Engineering-3/RCMx1/board/RCMX Rev_00_BPS2_sch.pdf

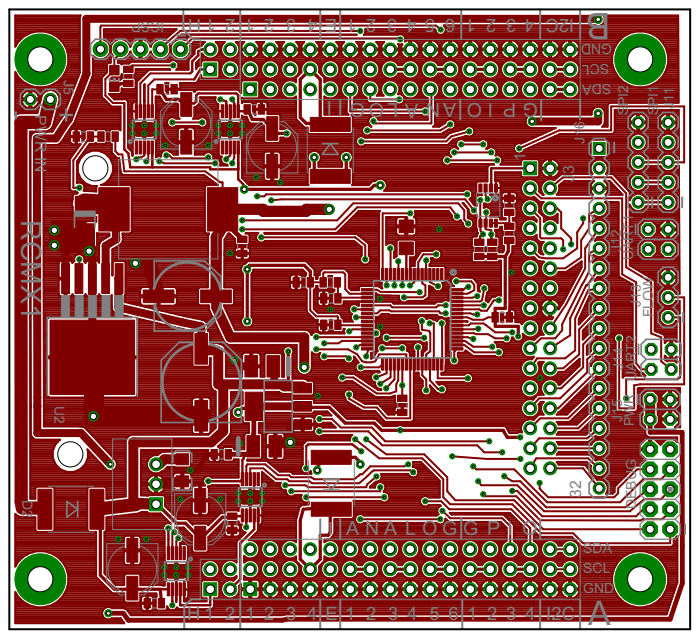
[picture p8: page 1]

J3 1 32 4G DNG LCS ADS 1 A SDA SCL GND RCMX1 -+ 2 6 1 1 I 3 4 5 4 1 2 3 4 E 1 3 4 5 1 2 3 G L NA OI P 2 4 E 2 3 6 2 3 N A L O G G P I O I O A 1 2 H 1 2 H I2CC2I PSCI PWR IN DEBUG PWR UART2 FLOW UART1 SPI2 SPI1 BA U2 J11 J5 J12 J13 J14 J15 J16 D2
