Engineering-3/RCMx1/board/RCMX Rev_00_BPS_brd.pdf

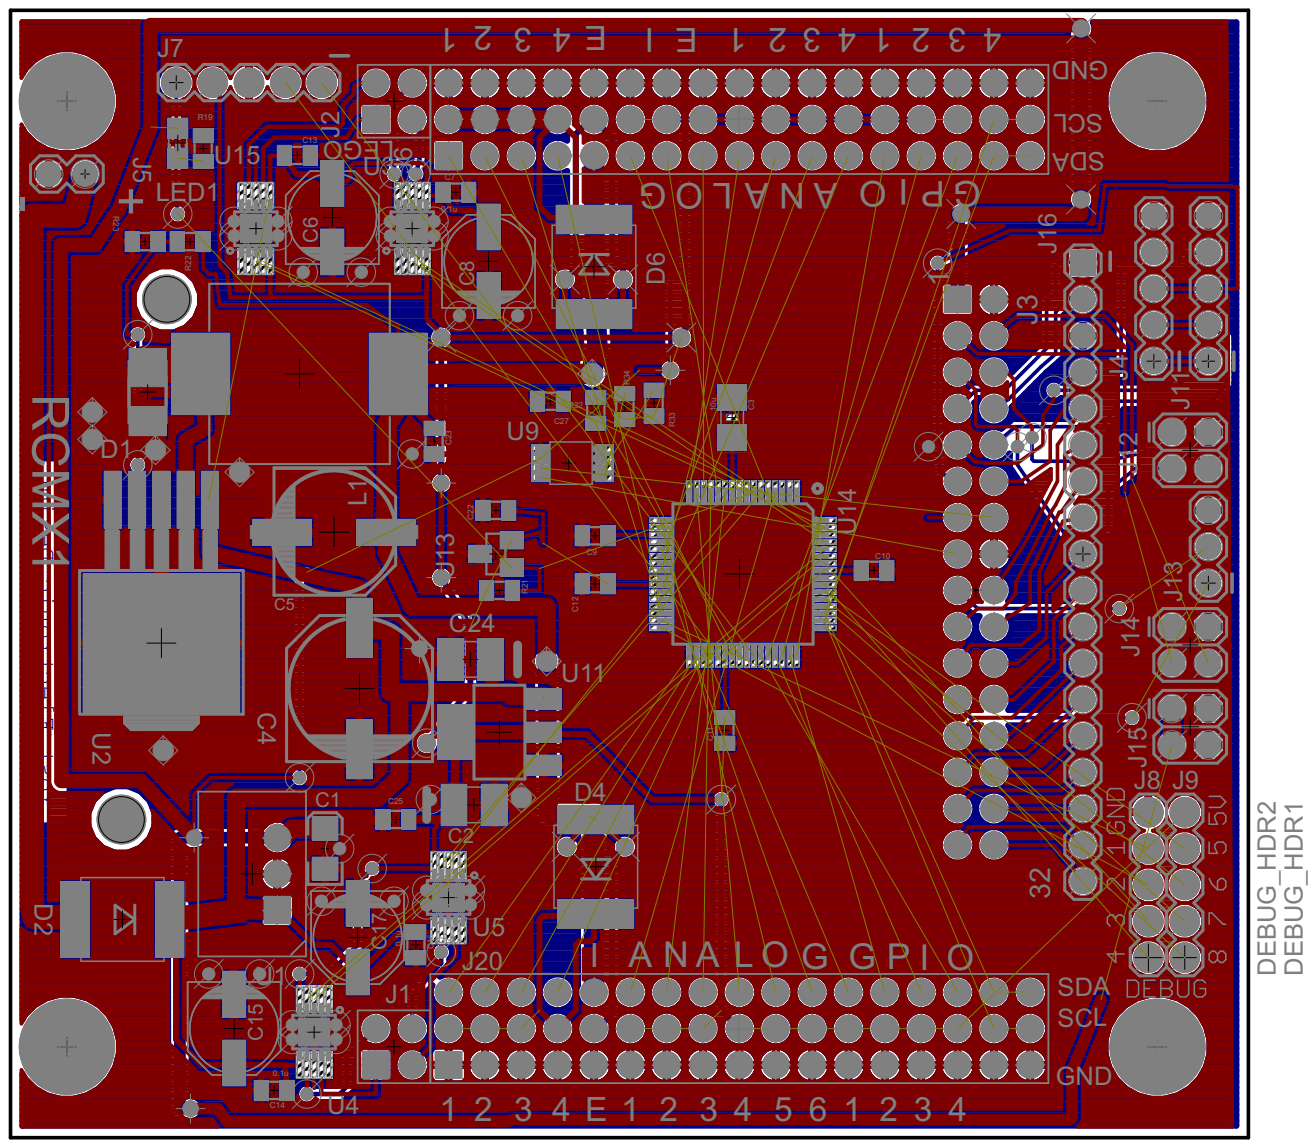
[picture p9: page 1]
