Engineering-3/RCMx1/board/RCMX Rev_00_BPS_NewSilk_silk.pdf

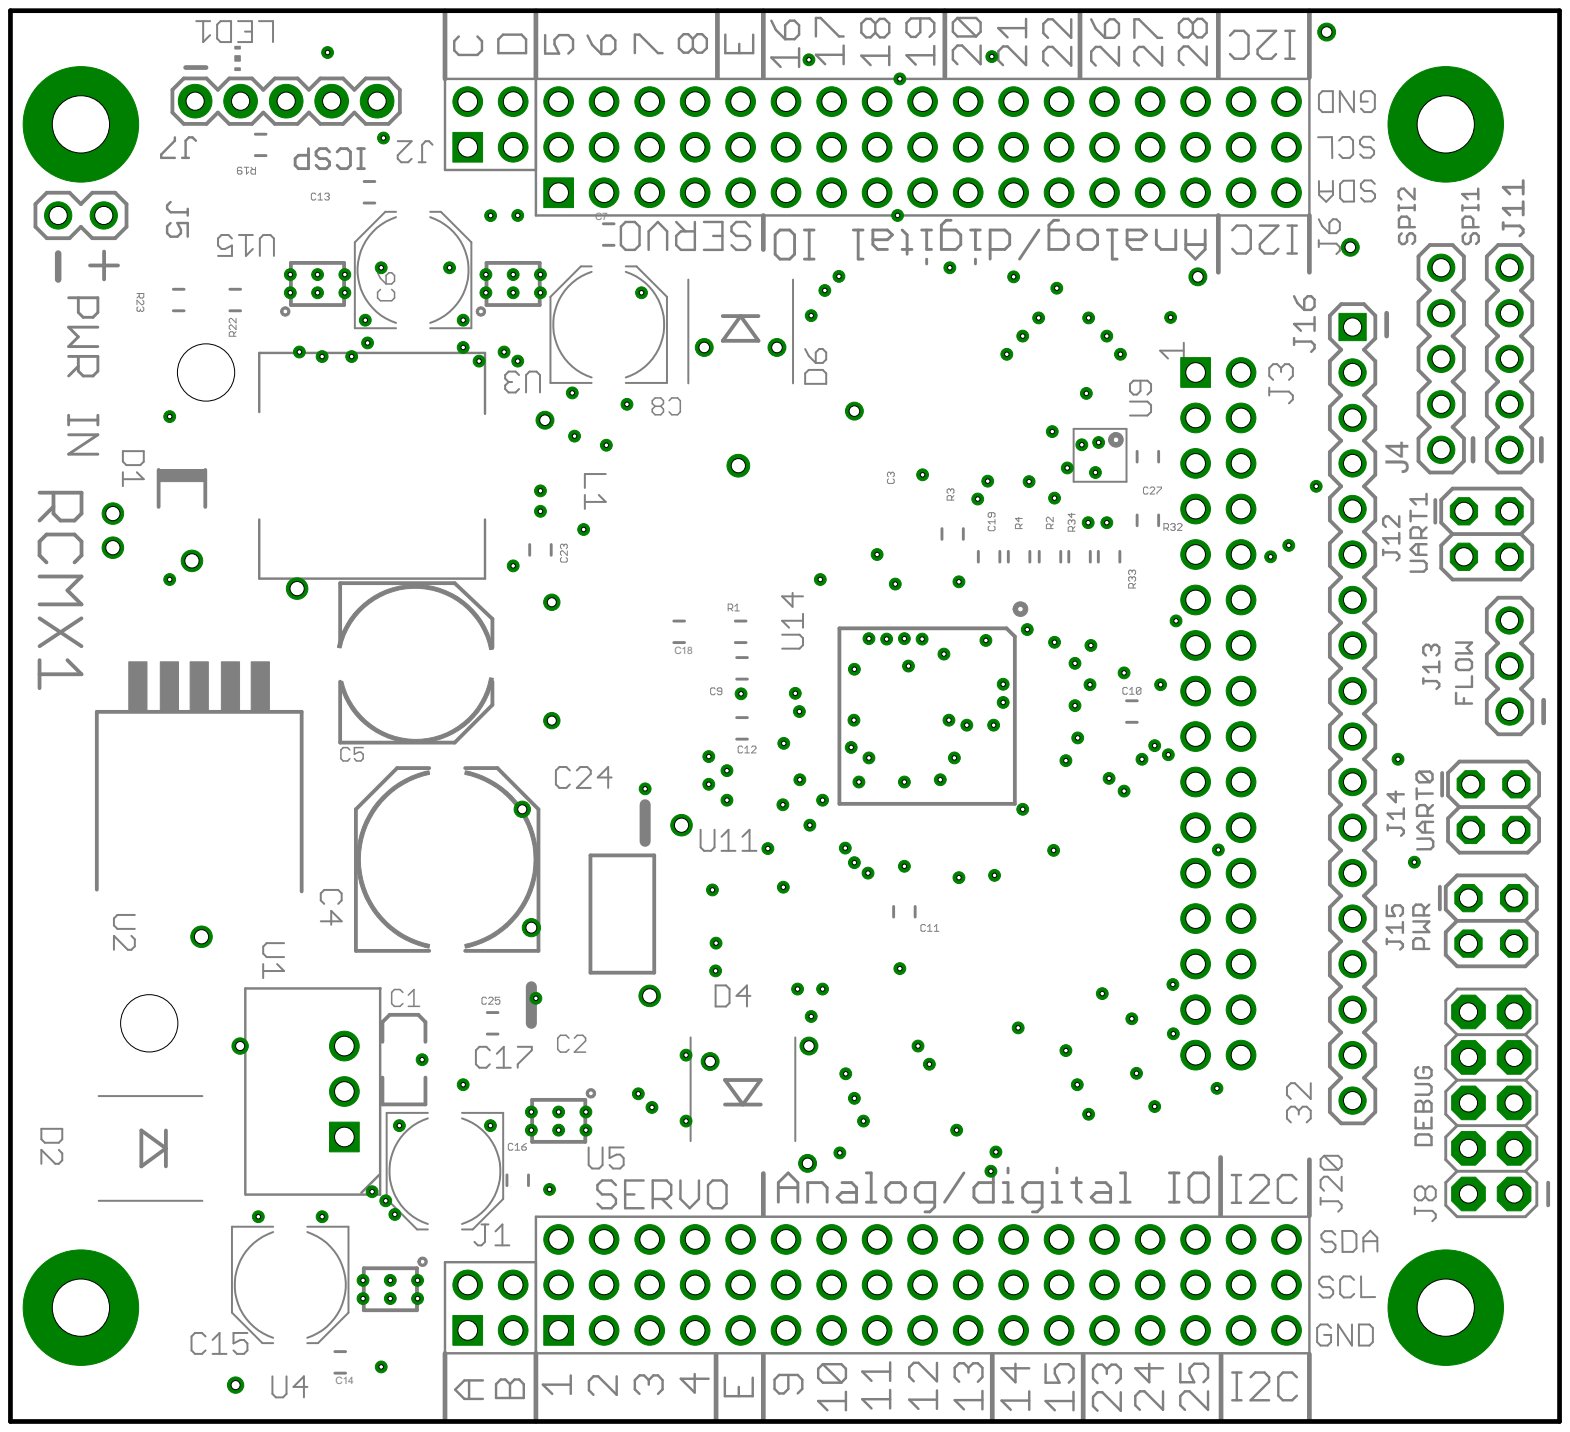
[picture p10: page 1]
