Engineering-3/RCMx1/board/RCMx1_v04/RCMx1 Rev_04_brd.pdf

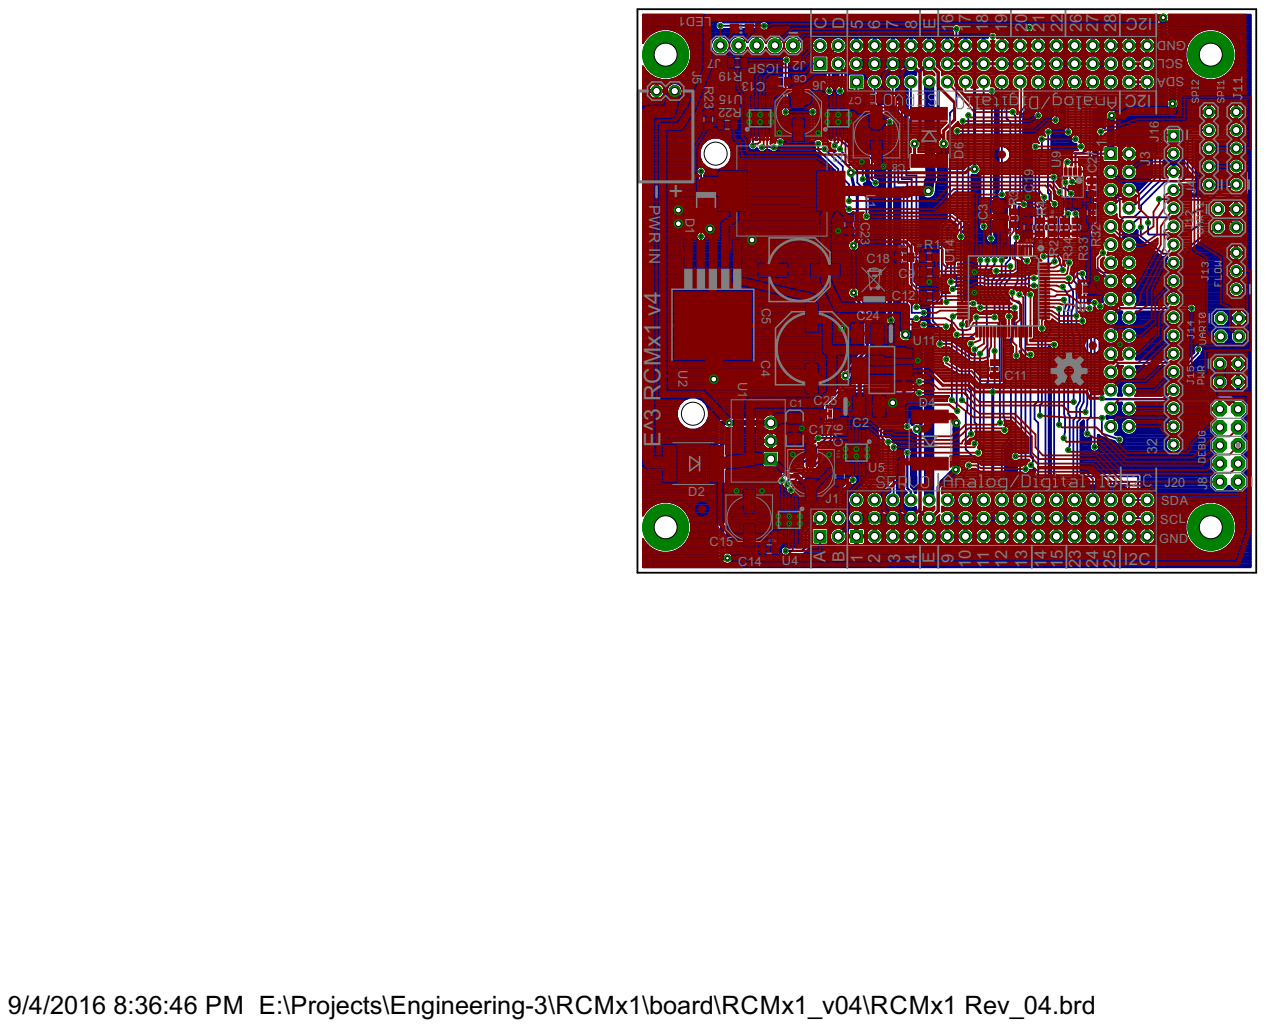
[picture p11: page 1]

9/4/2016 8:36:46 PM E:\Projects\Engineering-3\RCMx1\board\RCMx1_v04\RCMx1 Rev_04.brd
