Engineering-3/RCMx1/board/RCMx1_v04/RCMx1 Rev_04_sch.pdf

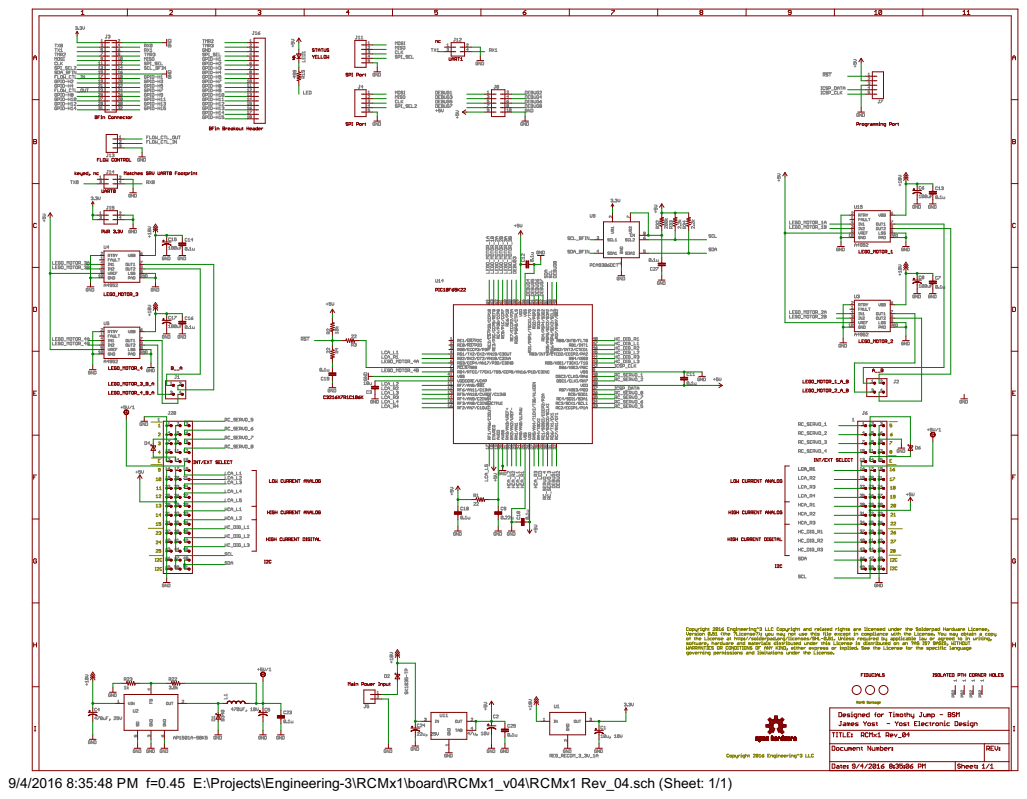
[picture p12: page 1]

9/4/2016 8:35:48 PM f=0.45 E:\Projects\Engineering-3\RCMx1\board\RCMx1_v04\RCMx1 Rev_04.sch (Sheet: 1/1)
