Engineering-3/RCMx1/board/RCMx1_v01/RCMX Rev_01 Silk.pdf

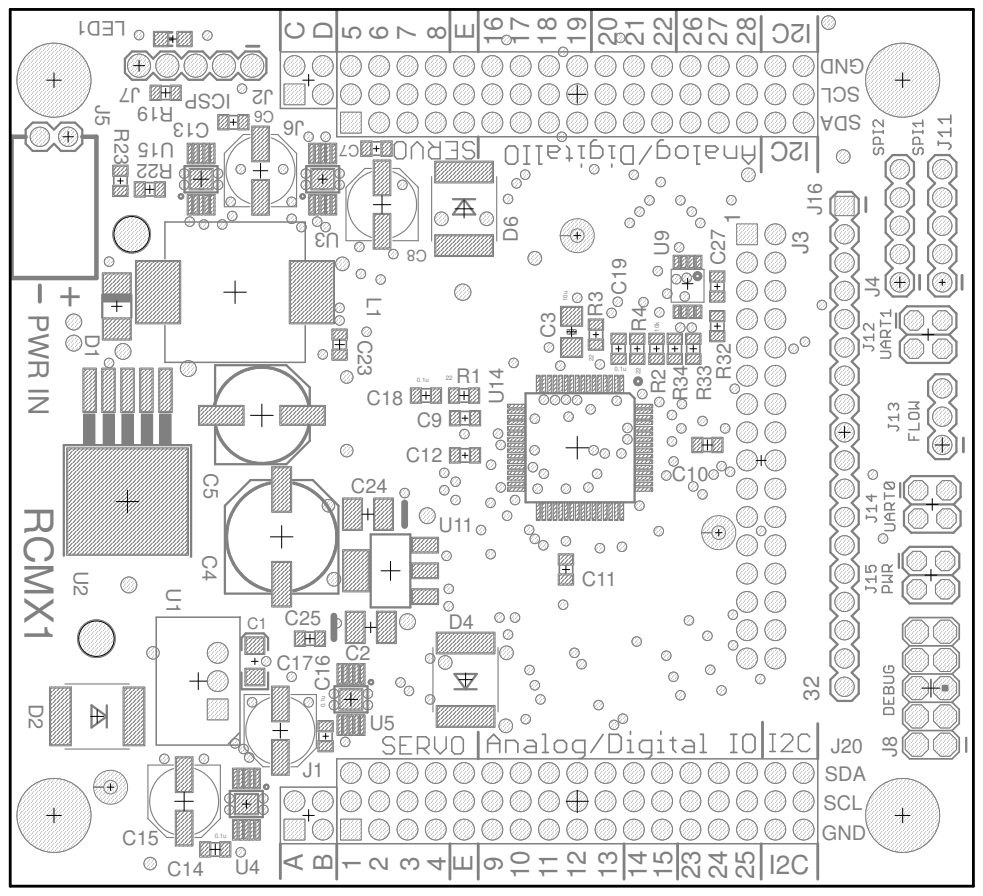
[picture p13: page 1]
