Engineering-3/RCMx1/firmware/src/RCMx1.X/system.c

/******************************************************************************
 * RCMx1 Firmware
 * Written for Tim Jump at Engineering^3
 * By Brian Schmalz of LogicPD
 * July 2012
 * Copyright Engineering^3 2015
 *
 * This firmware runs all of the functions of the RCMx1 I/O expander board
 * The RXMx1 connects to the SRV-1 Surveyor Blackfin Camera board via I2C
 * and listens for commands from the SRV. It has analog inputs, digital I/O,
 * RC Servo outputs, and h-bridge motor driver outputs. It also breaks out all
 * of the SRV-1 bus signals.
 *
 *
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
 * You should have received a copy of the GNU General Public License
 * along with this program; if not, write to the Free Software
 * Foundation, Inc., 51 Franklin Street, Fifth Floor, Boston, MA  02110-1301, USA.
 *****************************************************************************/

/******************************************************************************/
/*Files to Include                                                            */
/******************************************************************************/

#include <p18f86k22.h>
#include <GenericTypeDefs.h>
#include "system.h"
#include "user.h"

// List the actual analog input channel numbers in pin order (from pin 1
// through pin 14)
const UINT8 AnalogPinMap[14] = {19, 5, 10, 8, 6, 1, 3, 18, 11, 9, 7, 0, 2, 4};

/* Config bit settings */
#pragma config RETEN = OFF
#pragma config INTOSCSEL = LOW
#pragma config SOSCSEL = DIG
#pragma config XINST = OFF
#pragma config FOSC = INTIO2
#pragma config PLLCFG = ON
#pragma config FCMEN = OFF
#pragma config IESO = ON
#pragma config PWRTEN = OFF
#pragma config BOREN = ON
#pragma config BORV = 0
#pragma config BORPWR = LOW
#pragma config WDTEN = OFF
#pragma config WDTPS = 1
#pragma config RTCOSC = INTOSCREF
#pragma config CCP2MX = PORTBE
#pragma config MSSPMSK = MSK7
#pragma config MCLRE = ON
#pragma config STVREN = OFF
#pragma config BBSIZ = BB1K
#pragma config DEBUG = ON
#pragma config CP0 = OFF
#pragma config CP1 = OFF
#pragma config CP2 = OFF
#pragma config CP3 = OFF
#pragma config CPB = OFF
#pragma config CPD = OFF
#pragma config WRT0 = OFF
#pragma config WRT1 = OFF
#pragma config WRT2 = OFF
#pragma config WRT3 = OFF
#pragma config WRTC = OFF
#pragma config WRTB = OFF
#pragma config WRTD = OFF
#pragma config EBRT0 = OFF
#pragma config EBRT1 = OFF
#pragma config EBRT2 = OFF
#pragma config EBRT3 = OFF
#pragma config EBRTB = OFF


/* Refer to the device datasheet for information about available
oscillator configurations. */
void ConfigureOscillator(void)
{
    // Use 16Mhz from internal oscillator
    OSCCONbits.IRCF = 0b111;
    
    // Turn on the PLL
    OSCTUNEbits.PLLEN = 1;
}

void IOInit(void)
{
    // Set up TRIS bits for entire system
    // See RCMx1 PinTable.xls
    TRISA = 0x2F;
    TRISB = 0xFF;
    TRISC = 0xC0;       // 0b11000000
    TRISD = 0x6F;
    TRISE = 0x03;
    TRISF = 0xFF;
    TRISG = 0x27;

    INTCON2bits.RBPU = GPIO_PULLUP_DISABLE;
    GPIO_PullUp = 0;
    
    // For debug
    DEBUG1_TRIS = OUTPUT;
    DEBUG2_TRIS = OUTPUT;
    DEBUG3_TRIS = OUTPUT;
    DEBUG4_TRIS = OUTPUT;
    DEBUG5_TRIS = OUTPUT;
    DEBUG6_TRIS = OUTPUT;
    DEBUG7_TRIS = OUTPUT;
    DEBUG8_TRIS = OUTPUT;

    DEBUG1 = 0;
    DEBUG2 = 0;
    DEBUG3 = 0;
    DEBUG4 = 0;
    DEBUG5 = 0;
    DEBUG6 = 0;
    DEBUG7 = 0;
    DEBUG8 = 0;
}

// Take an internal representation register of the GPIO pins,
// and convert to the actual bit positions for outputting to a port
UINT8 GPIOPinMapOut(UINT8 Input)
{
    UINT8 Result = 0;

    if (Input & 0x01)
    {
        Result |= GPIO1_BIT;
    }
    if (Input & 0x02)
    {
        Result |= GPIO2_BIT;
    }
    if (Input & 0x04)
    {
        Result |= GPIO3_BIT;
    }
    if (Input & 0x08)
    {
        Result |= GPIO4_BIT;
    }
    if (Input & 0x10)
    {
        Result |= GPIO5_BIT;
    }
    if (Input & 0x20)
    {
        Result |= GPIO6_BIT;
    }
    return Result;
}

// Reading from GPIO pins, mapping to internal register bits
UINT8 GPIOPinMapIn(UINT8 Input)
{
    UINT8 Result = 0;

    if (Input & GPIO1_BIT)
    {
        Result |= 0x01;
    }
    if (Input & GPIO2_BIT)
    {
        Result |= 0x02;
    }
    if (Input & GPIO3_BIT)
    {
        Result |= 0x04;
    }
    if (Input & GPIO4_BIT)
    {
        Result |= 0x08;
    }
    if (Input & GPIO5_BIT)
    {
        Result |= 0x10;
    }
    if (Input & GPIO6_BIT)
    {
        Result |= 0x20;
    }
    return Result;
}

// Modify Input by GPIO invert bits and return value
UINT8 GPIOInvert(UINT8 Input)
{
    return (Input ^ GPIO_Invert);
}

// Read the TRIS bits for RCServo bits
UINT8 RCServoGPIOReadDirection(void)
{
    UINT8 Result = 0;
    if (RCSERVO1_TRIS == 1)
    {
        Result = Result | 0x01;
    }
    if (RCSERVO2_TRIS == 1)
    {
        Result = Result | 0x02;
    }
    if (RCSERVO3_TRIS == 1)
    {
        Result = Result | 0x04;
    }
    if (RCSERVO4_TRIS == 1)
    {
        Result = Result | 0x08;
    }
    if (RCSERVO5_TRIS == 1)
    {
        Result = Result | 0x10;
    }
    if (RCSERVO6_TRIS == 1)
    {
        Result = Result | 0x20;
    }
    if (RCSERVO7_TRIS == 1)
    {
        Result = Result | 0x40;
    }
    if (RCSERVO8_TRIS == 1)
    {
        Result = Result | 0x80;
    }

    return Result;
}

// Write the TRIS bits for RCServo bits, except if bit is in RC Servo mode,
// then make sure TRIS is set as an output
void RCServoGPIOWriteDirection(UINT8 Input)
{
    if (RCServo_Enable[0] == RC_SERVO_ENABLE_OFF)
    {
        if ((Input & 0x01) == RC_SERVO_DIRECTION_INPUT)
        {
            RCSERVO1_TRIS = INPUT;
        }
        else
        {
            RCSERVO1_TRIS = OUTPUT;
        }
    }
    else
    {
        RCSERVO1_TRIS = OUTPUT;
    }
    if (RCServo_Enable[1] == RC_SERVO_ENABLE_OFF)
    {
        if (((Input & 0x02) >> 1) == RC_SERVO_DIRECTION_INPUT)
        {
            RCSERVO2_TRIS = INPUT;
        }
        else
        {
            RCSERVO2_TRIS = OUTPUT;
        }
    }
    else
    {
        RCSERVO2_TRIS = OUTPUT;
    }
    if (RCServo_Enable[2] == RC_SERVO_ENABLE_OFF)
    {
        if (((Input & 0x04) >> 2) == RC_SERVO_DIRECTION_INPUT)
        {
            RCSERVO3_TRIS = INPUT;
        }
        else
        {
            RCSERVO3_TRIS = OUTPUT;
        }
    }
    else
    {
        RCSERVO3_TRIS = OUTPUT;
    }
    if (RCServo_Enable[3] == RC_SERVO_ENABLE_OFF)
    {
        if (((Input & 0x08) >> 3) == RC_SERVO_DIRECTION_INPUT)
        {
            RCSERVO4_TRIS = INPUT;
        }
        else
        {
            RCSERVO4_TRIS = OUTPUT;
        }
    }
    else
    {
        RCSERVO4_TRIS = OUTPUT;
    }
    if (RCServo_Enable[4] == RC_SERVO_ENABLE_OFF)
    {
        if (((Input & 0x10) >> 4) == RC_SERVO_DIRECTION_INPUT)
        {
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
    {
        ANALOG14_ENABLE = ANALOG_ENABLE;
    }
    else
    {
        ANALOG14_ENABLE = ANALOG_DISABLE;
    }

    Analog_Enable[0] = Low;
    Analog_Enable[1] = High;
    AnalogGPIOWriteDirection(Analog_Dir[0], Analog_Dir[1]);
}

// Take in an analog pin number - 1 (0 through 13)
// return the PIC analog channel assigned to that pin
UINT8 AnalogChannelMap(UINT8 Input)
{
    return(AnalogPinMap[Input]);
}
